CaratacusPotts/Matrix-Sequencer/MatrixV2/Atmel/adafruit_products_ItsyBitsy_M0_sch.png

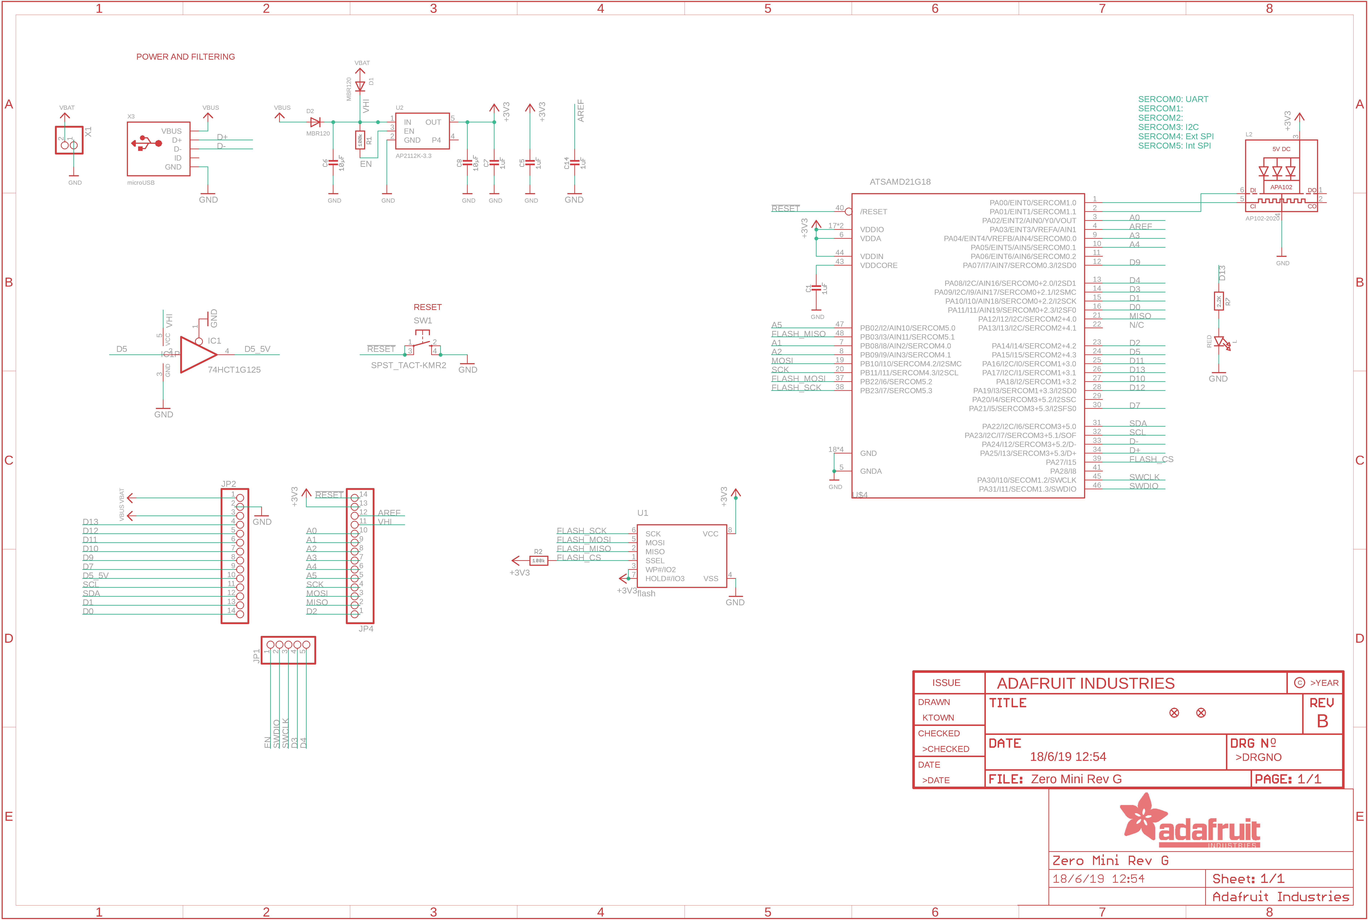
MatrixV2/Atmel/adafruit_products_ItsyBitsy_M0_sch.png
