CaratacusPotts/Matrix-Sequencer/MatrixV2/PCB/Matrix_V2_Base/Matrix_V2_Base.kicad_pcb

## KiCad design MatrixV2/PCB/Matrix_V2_Base/Matrix_V2_Base.kicad_pcb (2023-06-28)

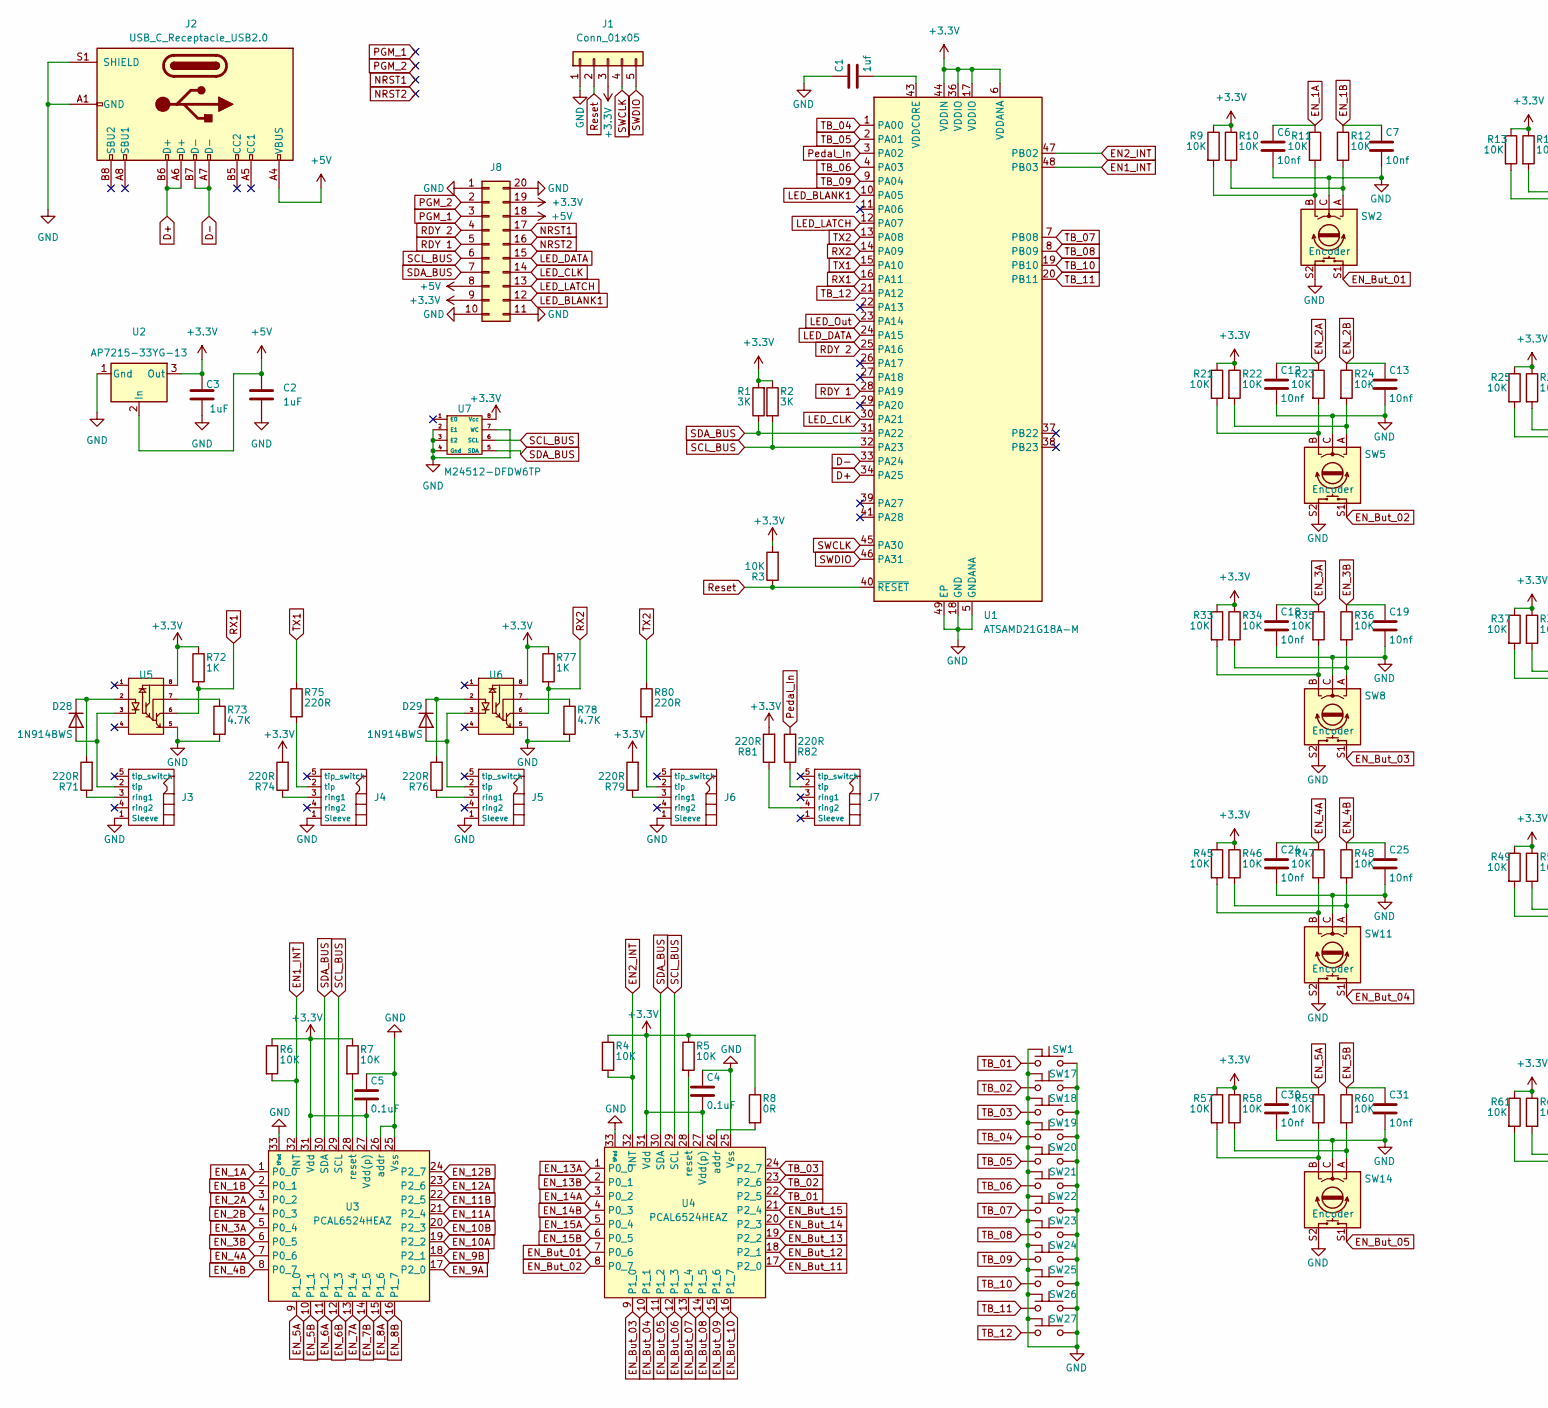
[picture p25: schematic Matrix_V2_Base.kicad_sch, part in row 1, column 1]

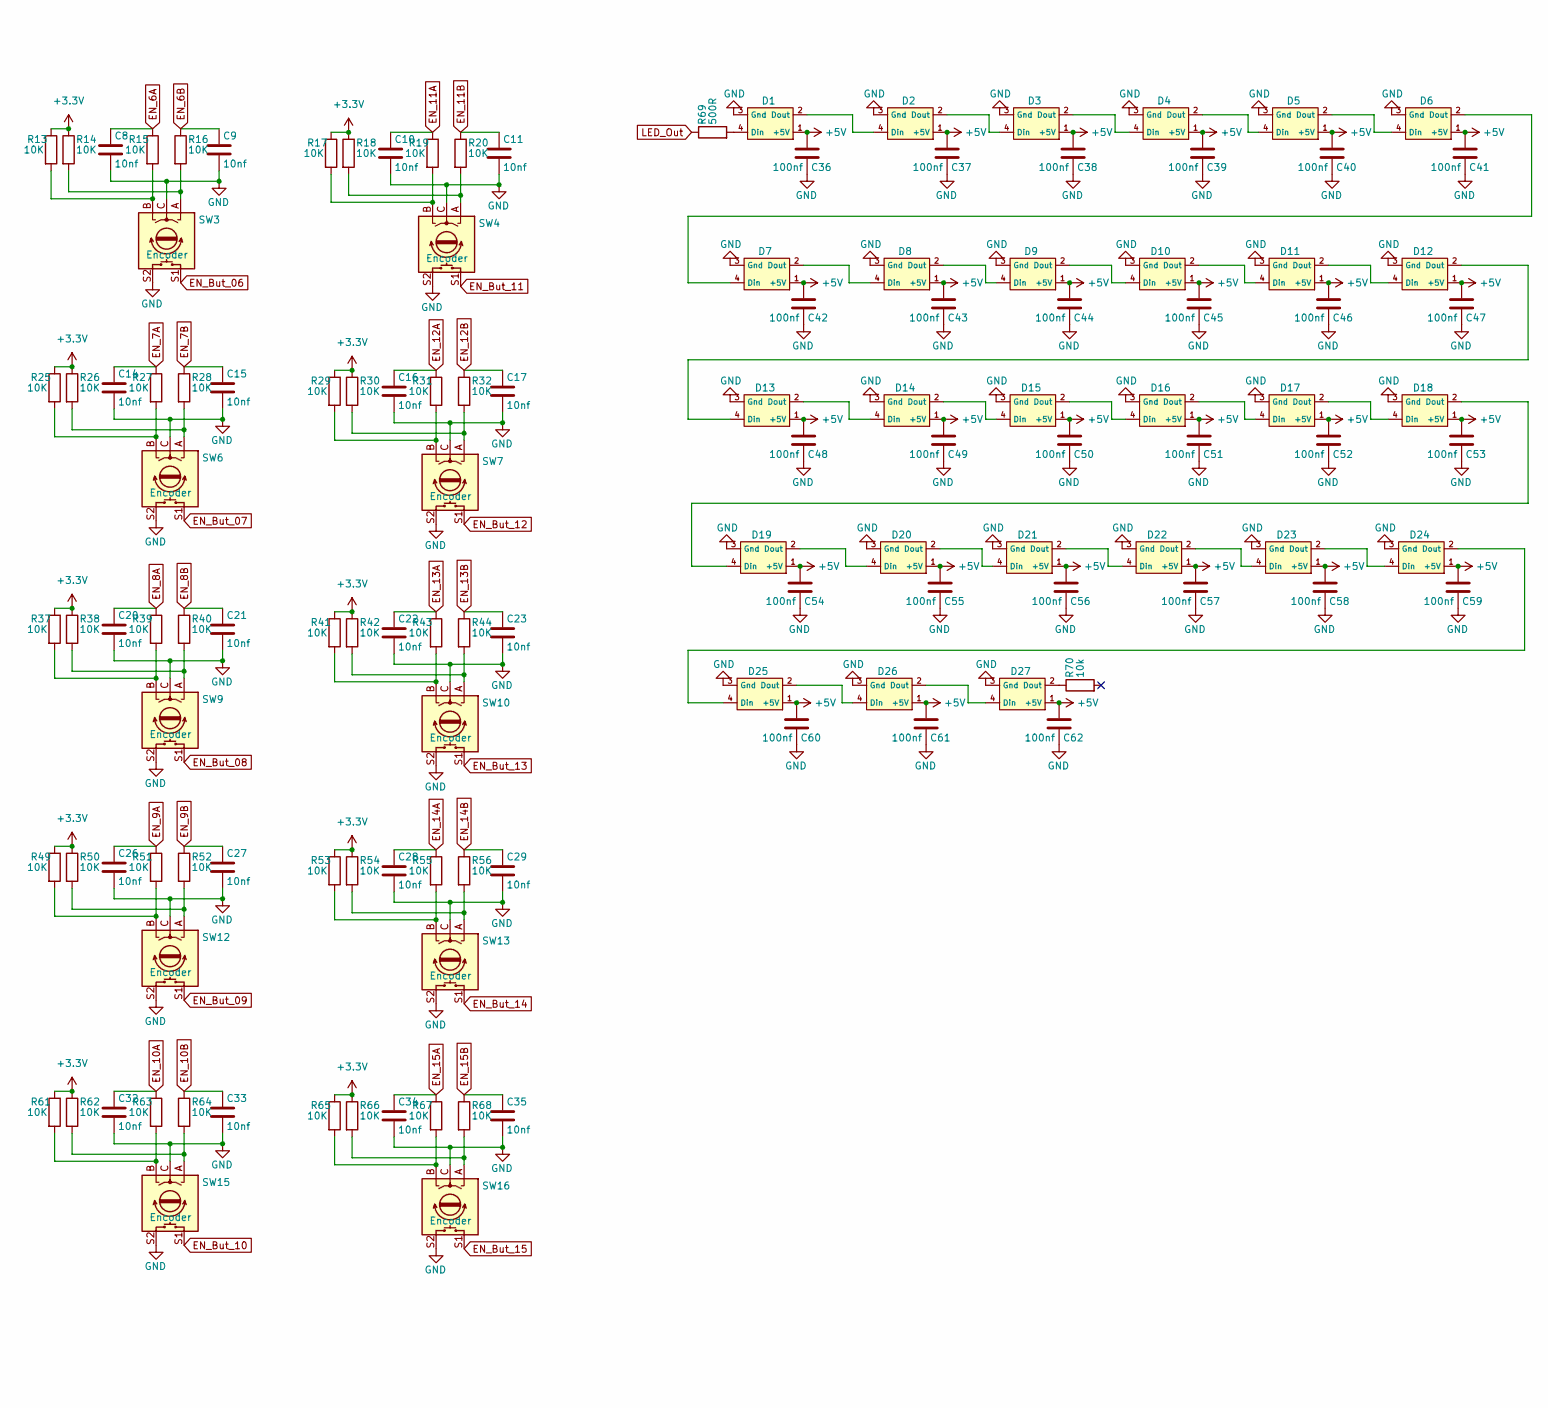
[picture p26: schematic Matrix_V2_Base.kicad_sch, part in row 1, column 2]

Parts:
C1: 1uf; C_0603_1608Metric_Pad1.08x0.95mm_HandSolder
C2, C3: 1uF; C_0603_1608Metric_Pad1.08x0.95mm_HandSolder
C4, C5: 0.1uF; C_0603_1608Metric_Pad1.08x0.95mm_HandSolder
C6, C7, C8, C9, C10, C11, C12, C13, C14, C15, C16, C17, C18, C19, C20, C21, C22, C23, C24, C25, C26, C27, C28, C29, C30, C31, C32, C33, C34, C35: 10nf; C_0603_1608Metric_Pad1.08x0.95mm_HandSolder
C36, C37, C38, C39, C40, C41, C42, C43, C44, C45, C46, C47, C48, C49, C50, C51, C52, C53, C54, C55, C56, C57, C58, C59, C60, C61, C62: 100nf; C_0603_1608Metric_Pad1.08x0.95mm_HandSolder
D1, D2, D3, D4, D5, D6, D7, D8, D9, D10, D11, D12, D13, D14, D15, D16, D17, D18, D19, D20, D21, D22, D23, D24, D25, D26, D27: IN-PI55TATPRPGPB
D28, D29: 1N914BWS; D_SOD-523
J1: Conn_01x05; 5pin SMD ProgramPads
J2: USB_C_Receptacle_USB2.0; USB_C_Receptacle_XKB_U262-16XN-4BVC11
J3, J4, J5, J6, J7: SJ-43515TS-SMT-TR
J8: Conn_02x10_Counter_Clockwise; 10132798-022100LF
R1, R2: 3K; R_0805_2012Metric_Pad1.20x1.40mm_HandSolder
R3, R4, R5, R6, R7, R9, R10, R11, R12, R13, R14, R15, R16, R17, R18, R19, R20, R21, R22, R23, R24, R25, R26, R27, R28, R29, R30, R31, R32, R33, R34, R35, R36, R37, R38, R39, R40, R41, R42, R43, R44, R45, R46, R47, R48, R49, R50, R51, R52, R53, R54, R55, R56, R57, R58, R59, R60, R61, R62, R63, R64, R65, R66, R67, R68: 10K; R_0805_2012Metric_Pad1.20x1.40mm_HandSolder
R8: 0R; R_0805_2012Metric_Pad1.20x1.40mm_HandSolder
R69: 500R; R_0805_2012Metric_Pad1.20x1.40mm_HandSolder
R70: 10k; R_0805_2012Metric_Pad1.20x1.40mm_HandSolder
R71, R74, R75, R76, R79, R80, R81, R82: 220R; R_0805_2012Metric_Pad1.20x1.40mm_HandSolder
R72, R77: 1K; R_0805_2012Metric_Pad1.20x1.40mm_HandSolder
R73, R78: 4.7K; R_0805_2012Metric_Pad1.20x1.40mm_HandSolder
SW1, SW17, SW18, SW19, SW20, SW21, SW22, SW23, SW24, SW25, SW26, SW27: SW_Push; TS06-667-55-BK-100-G-SMT-TR
SW2, SW3, SW4, SW5, SW6, SW7, SW8, SW9, SW10, SW11, SW12, SW13, SW14, SW15, SW16: Encoder; PEC11S
U1: ATSAMD21G18A-M; QFN-48-1EP_7x7mm_P0.5mm_EP5.15x5.15mm
U2: AP7215-33YG-13; SOT-89-3
U3, U4: PCAL6524HEAZ; HUQFN32
U5, U6: SFH6318; SFH6318 SOIC-8
U7: M24512-DFDW6TP

Connections:
+3.3V: C3.1, C4.2, C5.2, J1.3, J8.9, J8.19, R1.2, R2.1, R3.2, R4.1, R5.1, R6.1, R7.1, R8.1, R9.1, R10.1, R13.1, R14.1, R17.1, R18.1, R21.1, R22.1, R25.1, R26.1, R29.1, R30.1, R33.1, R34.1, R37.1, R38.1, R41.1, R42.1, R45.1, R46.1, R49.1, R50.1, R53.1, R54.1, R57.1, R58.1, R61.1, R62.1, R65.1, R66.1, R72.1, R74.2, R77.1, R79.2, R81.2, U1.6 (VDDANA), U1.17 (VDDIO), U1.36 (VDDIO), U1.44 (VDDIN), U2.3 (Out), U3.27 (Vdd(p)), U3.31 (Vdd), U4.27 (Vdd(p)), U4.31 (Vdd), U5.8, U6.8, U7.8 (Vcc)
+5V: C2.1, C36.1, C37.1, C38.1, C39.1, C40.1, C41.1, C42.1, C43.1, C44.1, C45.1, C46.1, C47.1, C48.1, C49.1, C50.1, C51.1, C52.1, C53.1, C54.1, C55.1, C56.1, C57.1, C58.1, C59.1, C60.1, C61.1, C62.1, D1.1 (+5V), D2.1 (+5V), D3.1 (+5V), D4.1 (+5V), D5.1 (+5V), D6.1 (+5V), D7.1 (+5V), D8.1 (+5V), D9.1 (+5V), D10.1 (+5V), D11.1 (+5V), D12.1 (+5V), D13.1 (+5V), D14.1 (+5V), D15.1 (+5V), D16.1 (+5V), D17.1 (+5V), D18.1 (+5V), D19.1 (+5V), D20.1 (+5V), D21.1 (+5V), D22.1 (+5V), D23.1 (+5V), D24.1 (+5V), D25.1 (+5V), D26.1 (+5V), D27.1 (+5V), J2.A4 (VBUS), J2.A9 (VBUS), J2.B4 (VBUS), J2.B9 (VBUS), J8.8, J8.18, U2.2 (In)
D+: J2.A6 (D+), J2.B6 (D+), U1.34 (PA25)
D-: J2.A7 (D-), J2.B7 (D-), U1.33 (PA24)
EN1_INT: R6.2, U1.48 (PB03), U3.32 (INT)
EN2_INT: R4.2, U1.47 (PB02), U4.32 (INT)
EN_1A: C6.1, R11.1, U3.1 (P0_0)
EN_1B: C7.1, R12.1, U3.2 (P0_1)
EN_2A: C12.1, R23.1, U3.3 (P0_2)
EN_2B: C13.1, R24.1, U3.4 (P0_3)
EN_3A: C18.1, R35.1, U3.5 (P0_4)
EN_3B: C19.1, R36.1, U3.6 (P0_5)
EN_4A: C24.1, R47.1, U3.7 (P0_6)
EN_4B: C25.1, R48.1, U3.8 (P0_7)
EN_5A: C30.1, R59.1, U3.9 (P1_0)
EN_5B: C31.1, R60.1, U3.10 (P1_1)
EN_6A: C8.1, R15.1, U3.11 (P1_2)
EN_6B: C9.1, R16.1, U3.12 (P1_3)
EN_7A: C14.1, R27.1, U3.13 (P1_4)
EN_7B: C15.1, R28.1, U3.14 (P1_5)
EN_8A: C20.1, R39.1, U3.15 (P1_6)
EN_8B: C21.1, R40.1, U3.16 (P1_7)
EN_9A: C26.1, R51.1, U3.17 (P2_0)
EN_9B: C27.1, R52.1, U3.18 (P2_1)
EN_10A: C32.1, R63.1, U3.19 (P2_2)
EN_10B: C33.1, R64.1, U3.20 (P2_3)
EN_11A: C10.1, R19.1, U3.21 (P2_4)
EN_11B: C11.1, R20.1, U3.22 (P2_5)
EN_12A: C16.1, R31.1, U3.23 (P2_6)
EN_12B: C17.1, R32.1, U3.24 (P2_7)
EN_13A: C22.1, R43.1, U4.1 (P0_0)
EN_13B: C23.1, R44.1, U4.2 (P0_1)
EN_14A: C28.1, R55.1, U4.3 (P0_2)
EN_14B: C29.1, R56.1, U4.4 (P0_3)
EN_15A: C34.1, R67.1, U4.5 (P0_4)
EN_15B: C35.1, R68.1, U4.6 (P0_5)
EN_But_01: SW2.S1, U4.7 (P0_6)
EN_But_02: SW5.S1, U4.8 (P0_7)
EN_But_03: SW8.S1, U4.9 (P1_0)
EN_But_04: SW11.S1, U4.10 (P1_1)
EN_But_05: SW14.S1, U4.11 (P1_2)
EN_But_06: SW3.S1, U4.12 (P1_3)
EN_But_07: SW6.S1, U4.13 (P1_4)
EN_But_08: SW9.S1, U4.14 (P1_5)
EN_But_09: SW12.S1, U4.15 (P1_6)
EN_But_10: SW15.S1, U4.16 (P1_7)
EN_But_11: SW4.S1, U4.17 (P2_0)
EN_But_12: SW7.S1, U4.18 (P2_1)
EN_But_13: SW10.S1, U4.19 (P2_2)
EN_But_14: SW13.S1, U4.20 (P2_3)
EN_But_15: SW16.S1, U4.21 (P2_4)
GND: C1.1, C2.2, C3.2, C4.1, C5.1, C6.2, C7.2, C8.2, C9.2, C10.2, C11.2, C12.2, C13.2, C14.2, C15.2, C16.2, C17.2, C18.2, C19.2, C20.2, C21.2, C22.2, C23.2, C24.2, C25.2, C26.2, C27.2, C28.2, C29.2, C30.2, C31.2, C32.2, C33.2, C34.2, C35.2, C36.2, C37.2, C38.2, C39.2, C40.2, C41.2, C42.2, C43.2, C44.2, C45.2, C46.2, C47.2, C48.2, C49.2, C50.2, C51.2, C52.2, C53.2, C54.2, C55.2, C56.2, C57.2, C58.2, C59.2, C60.2, C61.2, C62.2, D1.3 (Gnd), D2.3 (Gnd), D3.3 (Gnd), D4.3 (Gnd), D5.3 (Gnd), D6.3 (Gnd), D7.3 (Gnd), D8.3 (Gnd), D9.3 (Gnd), D10.3 (Gnd), D11.3 (Gnd), D12.3 (Gnd), D13.3 (Gnd), D14.3 (Gnd), D15.3 (Gnd), D16.3 (Gnd), D17.3 (Gnd), D18.3 (Gnd), D19.3 (Gnd), D20.3 (Gnd), D21.3 (Gnd), D22.3 (Gnd), D23.3 (Gnd), D24.3 (Gnd), D25.3 (Gnd), D26.3 (Gnd), D27.3 (Gnd), J1.1, J2.A1 (GND), J2.A12 (GND), J2.B1 (GND), J2.B12 (GND), J2.S1 (SHIELD), J3.1 (Sleeve), J4.1 (Sleeve), J5.1 (Sleeve), J6.1 (Sleeve), J8.1, J8.10, J8.11, J8.20, R73.2, R78.2, SW1.2, SW1.3 (GND), SW2.C, SW2.S2, SW3.C, SW3.S2, SW4.C, SW4.S2, SW5.C, SW5.S2, SW6.C, SW6.S2, SW7.C, SW7.S2, SW8.C, SW8.S2, SW9.C, SW9.S2, SW10.C, SW10.S2, SW11.C, SW11.S2, SW12.C, SW12.S2, SW13.C, SW13.S2, SW14.C, SW14.S2, SW15.C, SW15.S2, SW16.C, SW16.S2, SW17.2, SW17.3 (GND), SW18.2, SW18.3 (GND), SW19.2, SW19.3 (GND), SW20.2, SW20.3 (GND), SW21.2, SW21.3 (GND), SW22.2, SW22.3 (GND), SW23.2, SW23.3 (GND), SW24.2, SW24.3 (GND), SW25.2, SW25.3 (GND), SW26.2, SW26.3 (GND), SW27.2, SW27.3 (GND), U1.5 (GNDANA), U1.18 (GND), U1.35 (GND), U1.42 (GND), U1.49 (EP), U2.1 (Gnd), U3.25 (Vss), U3.26 (addr), U3.33 (tPad), U4.25 (Vss), U4.33 (tPad), U5.5, U6.5, U7.2 (E1), U7.3 (E2), U7.4 (Gnd), U7.7 (WC)
LED_BLANK1: J8.12, U1.10 (PA05)
LED_CLK: J8.14, U1.30 (PA21)
LED_DATA: J8.15, U1.24 (PA15)
LED_LATCH: J8.13, U1.12 (PA07)
LED_Out: R69.1, U1.23 (PA14)
NRST1: J8.17
NRST2: J8.16
unnamed: C1.2, U1.43 (VDDCORE)
unnamed: D1.2 (Dout), D2.4 (Din)
unnamed: D1.4 (Din), R69.2
unnamed: D2.2 (Dout), D3.4 (Din)
unnamed: D3.2 (Dout), D4.4 (Din)
unnamed: D4.2 (Dout), D5.4 (Din)
unnamed: D5.2 (Dout), D6.4 (Din)
unnamed: D6.2 (Dout), D7.4 (Din)
unnamed: D7.2 (Dout), D8.4 (Din)
unnamed: D8.2 (Dout), D9.4 (Din)
unnamed: D10.2 (Dout), D11.4 (Din)
unnamed: D9.2 (Dout), D10.4 (Din)
unnamed: D11.2 (Dout), D12.4 (Din)
unnamed: D12.2 (Dout), D13.4 (Din)
unnamed: D13.2 (Dout), D14.4 (Din)
unnamed: D14.2 (Dout), D15.4 (Din)
unnamed: D15.2 (Dout), D16.4 (Din)
unnamed: D16.2 (Dout), D17.4 (Din)
unnamed: D17.2 (Dout), D18.4 (Din)
unnamed: D18.2 (Dout), D19.4 (Din)
unnamed: D19.2 (Dout), D20.4 (Din)
unnamed: D20.2 (Dout), D21.4 (Din)
unnamed: D21.2 (Dout), D22.4 (Din)
unnamed: D22.2 (Dout), D23.4 (Din)
unnamed: D23.2 (Dout), D24.4 (Din)
unnamed: D24.2 (Dout), D25.4 (Din)
unnamed: D25.2 (Dout), D26.4 (Din)
unnamed: D26.2 (Dout), D27.4 (Din)
unnamed: D27.2 (Dout), R70.1
unnamed: D28.1 (K), R71.2, U5.2
unnamed: D28.2 (A), J3.2 (tip), U5.3
unnamed: D29.1 (K), R76.2, U6.2
unnamed: D29.2 (A), J5.2 (tip), U6.3
unnamed: J3.3 (ring1), R71.1
unnamed: J4.2 (tip), R75.2
unnamed: J4.3 (ring1), R74.1
unnamed: J5.3 (ring1), R76.1
unnamed: J6.2 (tip), R80.2
unnamed: J6.3 (ring1), R79.1
unnamed: J7.2 (tip), R82.1
unnamed: J7.4 (ring2), R81.1
unnamed: R5.2, U4.28 (reset)
unnamed: R7.2, U3.28 (reset)
unnamed: R8.2, U4.26 (addr)
unnamed: R10.2, R12.2, SW2.A
unnamed: R9.2, R11.2, SW2.B
unnamed: R13.2, R15.2, SW3.B
unnamed: R14.2, R16.2, SW3.A
unnamed: R17.2, R19.2, SW4.B
unnamed: R18.2, R20.2, SW4.A
unnamed: R21.2, R23.2, SW5.B
unnamed: R22.2, R24.2, SW5.A
unnamed: R25.2, R27.2, SW6.B
unnamed: R26.2, R28.2, SW6.A
unnamed: R29.2, R31.2, SW7.B
unnamed: R30.2, R32.2, SW7.A
unnamed: R33.2, R35.2, SW8.B
unnamed: R34.2, R36.2, SW8.A
unnamed: R37.2, R39.2, SW9.B
unnamed: R38.2, R40.2, SW9.A
unnamed: R41.2, R43.2, SW10.B
unnamed: R42.2, R44.2, SW10.A
unnamed: R45.2, R47.2, SW11.B
unnamed: R46.2, R48.2, SW11.A
unnamed: R49.2, R51.2, SW12.B
unnamed: R50.2, R52.2, SW12.A
unnamed: R53.2, R55.2, SW13.B
unnamed: R54.2, R56.2, SW13.A
unnamed: R57.2, R59.2, SW14.B
unnamed: R58.2, R60.2, SW14.A
unnamed: R61.2, R63.2, SW15.B
unnamed: R62.2, R64.2, SW15.A
unnamed: R65.2, R67.2, SW16.B
unnamed: R66.2, R68.2, SW16.A
unnamed: R73.1, U5.7
unnamed: R78.1, U6.7
PGM_1: J8.3
PGM_2: J8.2
Pedal_In: R82.2, U1.3 (PA02)
RDY 1: J8.5, U1.28 (PA19)
RDY 2: J8.4, U1.25 (PA16)
RX1: R72.2, U1.16 (PA11), U5.6
RX2: R77.2, U1.14 (PA09), U6.6
Reset: J1.2, R3.1, U1.40 (~RESET)
SCL_BUS: J8.6, R2.2, U1.32 (PA23), U3.29 (SCL), U4.29 (SCL), U7.6 (SCL)
SDA_BUS: J8.7, R1.1, U1.31 (PA22), U3.30 (SDA), U4.30 (SDA), U7.5 (SDA)
SWCLK: J1.4, U1.45 (PA30)
SWDIO: J1.5, U1.46 (PA31)
TB_01: SW1.1, U4.22 (P2_5)
TB_02: SW17.1, U4.23 (P2_6)
TB_03: SW18.1, U4.24 (P2_7)
TB_04: SW19.1, U1.1 (PA00)
TB_05: SW20.1, U1.2 (PA01)
TB_06: SW21.1, U1.4 (PA03)
TB_07: SW22.1, U1.7 (PB08)
TB_08: SW23.1, U1.8 (PB09)
TB_09: SW24.1, U1.9 (PA04)
TB_10: SW25.1, U1.19 (PB10)
TB_11: SW26.1, U1.20 (PB11)
TB_12: SW27.1, U1.21 (PA12)
TX1: R75.1, U1.15 (PA10)
TX2: R80.1, U1.13 (PA08)

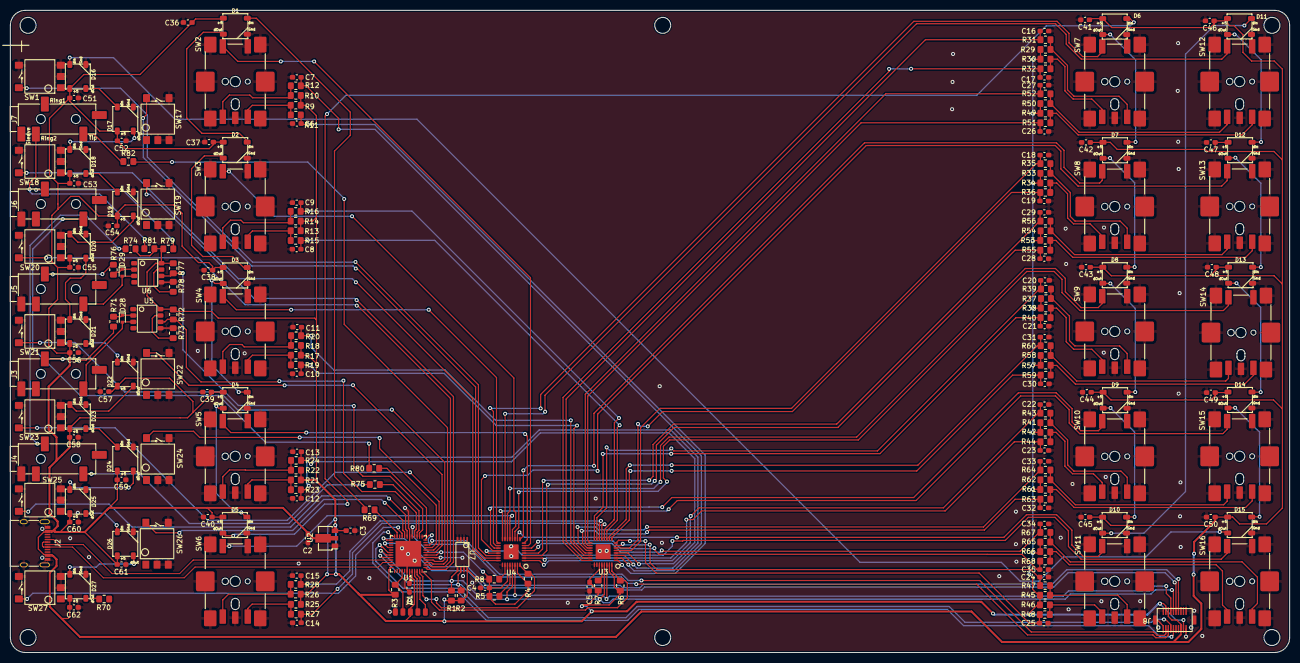
[picture p27: board Matrix_V2_Base.kicad_pcb from above]

Board: 2 copper layers, 256.0 x 128.5 mm, 215 parts (0 on the bottom side), 157 nets.
